NJCsih/NGC224/MK4/kicad/mk4-right/mk4-right.kicad_sch

## KiCad design MK4/kicad/mk4-right/mk4-right.kicad_sch (2026-01-11)

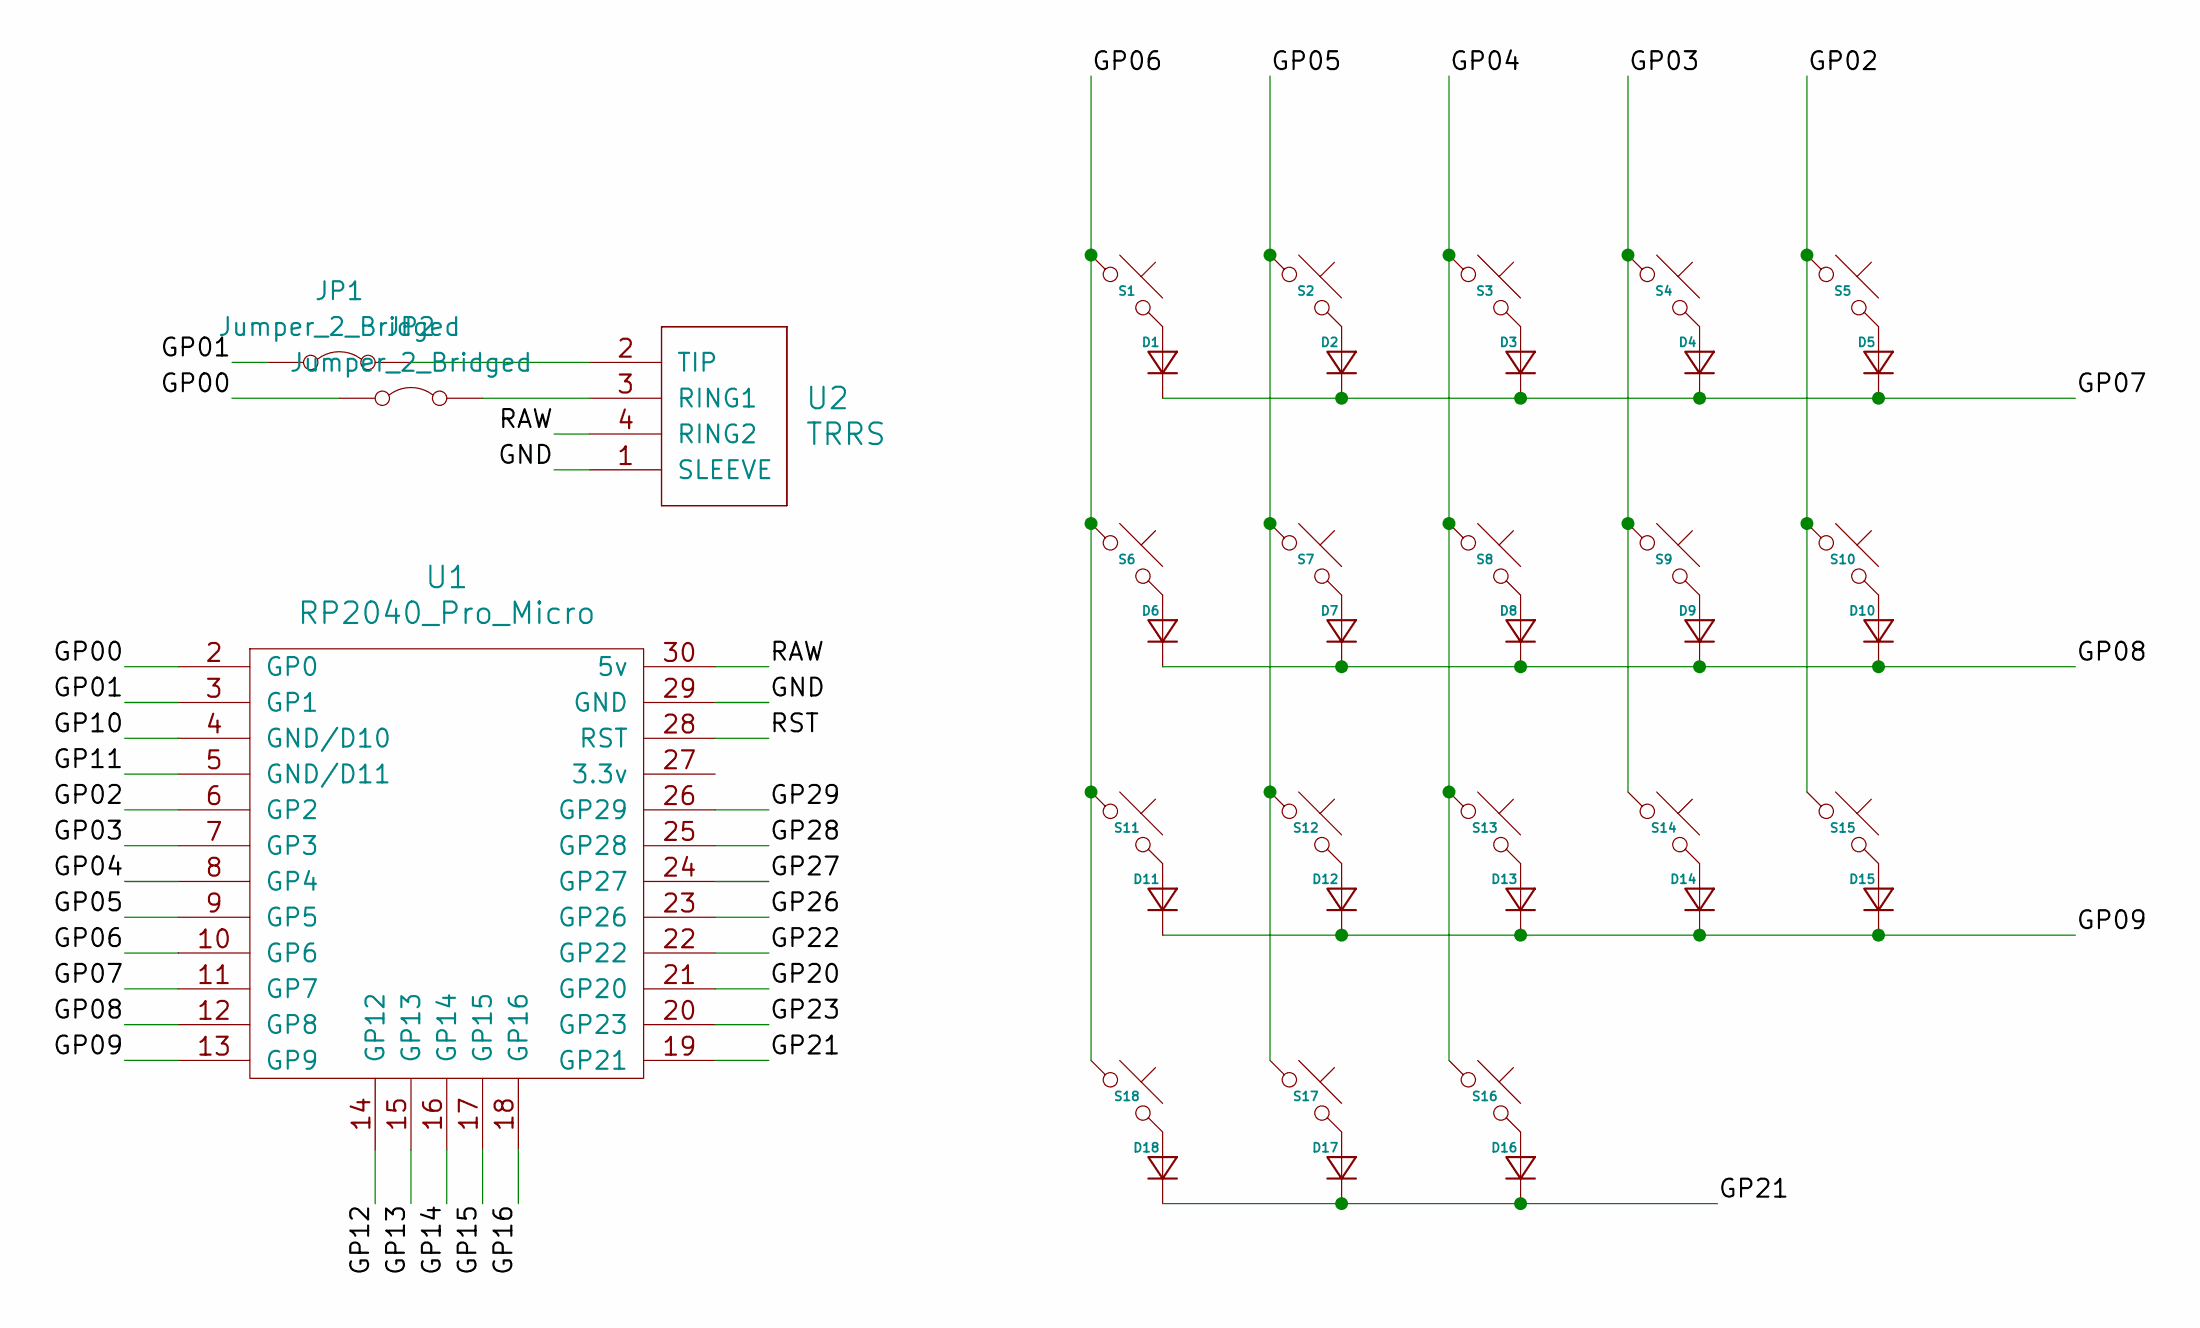
[picture p2: schematic mk4-right.kicad_sch]

Parts:
D1, D2, D3, D4, D5, D6, D7, D8, D9, D10, D11, D12, D13, D14, D15, D16, D17, D18: Diode_DO-35
JP1, JP2: Jumper_2_Bridged; SolderJumper-2_P1.3mm_Bridged_Pad1.0x1.5mm-tighter_courtyard
S1, S2, S3, S4, S5, S6, S7, S8, S9, S10, S11, S12, S13, S14, S15, S16, S17, S18: Choc_Hotswap_1.00u
U1: RP2040_Pro_Micro
U2: TRRS; TRRS_PJ-320A

Connections:
GND: U1.29 (GND), U2.1 (SLEEVE)
GP00: JP2.1 (A), U1.2 (GP0)
GP01: JP1.1 (A), U1.3 (GP1)
GP02: S5.1, S10.1, S15.1, U1.6 (GP2)
GP03: S4.1, S9.1, S14.1, U1.7 (GP3)
GP04: S3.1, S8.1, S13.1, S16.1, U1.8 (GP4)
GP05: S2.1, S7.1, S12.1, S17.1, U1.9 (GP5)
GP06: S1.1, S6.1, S11.1, S18.1, U1.10 (GP6)
GP07: D1.1 (K), D2.1 (K), D3.1 (K), D4.1 (K), D5.1 (K), U1.11 (GP7)
GP08: D6.1 (K), D7.1 (K), D8.1 (K), D9.1 (K), D10.1 (K), U1.12 (GP8)
GP09: D11.1 (K), D12.1 (K), D13.1 (K), D14.1 (K), D15.1 (K), U1.13 (GP9)
GP10: U1.4 (GND/D10)
GP11: U1.5 (GND/D11)
GP12: U1.14 (GP12)
GP13: U1.15 (GP13)
GP14: U1.16 (GP14)
GP15: U1.17 (GP15)
GP16: U1.18 (GP16)
GP20: U1.21 (GP20)
GP21: D16.1 (K), D17.1 (K), D18.1 (K), U1.19 (GP21)
GP22: U1.22 (GP22)
GP23: U1.20 (GP23)
GP26: U1.23 (GP26)
GP27: U1.24 (GP27)
GP28: U1.25 (GP28)
GP29: U1.26 (GP29)
unnamed: D1.2 (A), S1.2
unnamed: D2.2 (A), S2.2
unnamed: D3.2 (A), S3.2
unnamed: D4.2 (A), S4.2
unnamed: D5.2 (A), S5.2
unnamed: D6.2 (A), S6.2
unnamed: D7.2 (A), S7.2
unnamed: D8.2 (A), S8.2
unnamed: D9.2 (A), S9.2
unnamed: D10.2 (A), S10.2
unnamed: D11.2 (A), S11.2
unnamed: D12.2 (A), S12.2
unnamed: D13.2 (A), S13.2
unnamed: D14.2 (A), S14.2
unnamed: D15.2 (A), S15.2
unnamed: D16.2 (A), S16.2
unnamed: D17.2 (A), S17.2
unnamed: D18.2 (A), S18.2
unnamed: JP1.2 (B), U2.2 (TIP)
unnamed: JP2.2 (B), U2.3 (RING1)
RAW: U1.30 (5v), U2.4 (RING2)
RST: U1.28 (RST)
